liebman/esp32-gps-ntp/main/NTP.cpp

/*
 * MIT License
 *
 * Copyright (c) 2020 Christopher B. Liebman
 *
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
 * THE SOFTWARE IS PROVIDED "AS IS", WITHOUT WARRANTY OF ANY KIND, EXPRESS OR
 * IMPLIED, INCLUDING BUT NOT LIMITED TO THE WARRANTIES OF MERCHANTABILITY,
 * FITNESS FOR A PARTICULAR PURPOSE AND NONINFRINGEMENT. IN NO EVENT SHALL THE
 * AUTHORS OR COPYRIGHT HOLDERS BE LIABLE FOR ANY CLAIM, DAMAGES OR OTHER
 * LIABILITY, WHETHER IN AN ACTION OF CONTRACT, TORT OR OTHERWISE, ARISING FROM,
 * OUT OF OR IN CONNECTION WITH THE SOFTWARE OR THE USE OR OTHER DEALINGS IN THE
 * SOFTWARE.
*/

#include "NTP.h"
#include "Network.h"
#include "esp_log.h"
#include "math.h"

#include "lwip/err.h"
#include "lwip/sockets.h"
#include "lwip/sys.h"
#include <lwip/netdb.h>

static const char* TAG = "NTP";

//#define NTP_PACKET_DEBUG

#ifndef NTP_TASK_PRI
#define NTP_TASK_PRI configMAX_PRIORITIES-3
#endif

#ifndef NTP_TASK_CORE
#define NTP_TASK_CORE 1
#endif

//#define NTP_PACKET_DEBUG

#define NTP_PORT               123
#define PRECISION_COUNT        10000

typedef struct ntp_packet
{
    uint8_t  flags;
    uint8_t  stratum;
    uint8_t  poll;
    int8_t   precision;
    uint32_t delay;
    uint32_t dispersion;
    uint8_t  ref_id[4];
    NTPTime  ref_time;
    NTPTime  orig_time;
    NTPTime  recv_time;
    NTPTime  xmit_time;
} NTPPacket;

#define LI_NONE         0
#define LI_SIXTY_ONE    1
#define LI_FIFTY_NINE   2
#define LI_NOSYNC       3

#define MODE_RESERVED   0
#define MODE_ACTIVE     1
#define MODE_PASSIVE    2
#define MODE_CLIENT     3
#define MODE_SERVER     4
#define MODE_BROADCAST  5
#define MODE_CONTROL    6
#define MODE_PRIVATE    7

#define NTP_VERSION     4

#define REF_ID          "PPS "  // "GPS " when we have one!

#define setLI(value)    ((value&0x03)<<6)
#define setVERS(value)  ((value&0x07)<<3)
#define setMODE(value)  ((value&0x07))

#define getLI(value)    ((value>>6)&0x03)
#define getVERS(value)  ((value>>3)&0x07)
#define getMODE(value)  (value&0x07)

#define SEVENTY_YEARS   2208988800L
#define toEPOCH(t)      ((uint32_t)t-SEVENTY_YEARS)
#define toNTP(t)        ((uint32_t)t+SEVENTY_YEARS)

#ifdef NTP_PACKET_DEBUG
#include <time.h>
char* timestr(long int t)
{
    t = toEPOCH(t);
    return ctime(&t);
}

void dumpNTPPacket(NTPPacket* ntp)
{
    ESP_LOGI(TAG, "size:       %u", sizeof(*ntp));
    ESP_LOGI(TAG, "firstbyte:  0x%02x", *(uint8_t*)ntp);
    ESP_LOGI(TAG, "li:         %u", getLI(ntp->flags));
    ESP_LOGI(TAG, "version:    %u", getVERS(ntp->flags));
    ESP_LOGI(TAG, "mode:       %u", getMODE(ntp->flags));
    ESP_LOGI(TAG, "stratum:    %u", ntp->stratum);
    ESP_LOGI(TAG, "poll:       %u", ntp->poll);
    ESP_LOGI(TAG, "precision:  %d", ntp->precision);
    ESP_LOGI(TAG, "delay:      %u", ntp->delay);
    ESP_LOGI(TAG, "dispersion: %u", ntp->dispersion);
    ESP_LOGI(TAG, "ref_id:     %02x:%02x:%02x:%02x", ntp->ref_id[0], ntp->ref_id[1], ntp->ref_id[2], ntp->ref_id[3]);
    ESP_LOGI(TAG, "ref_time:   %08x:%08x", ntp->ref_time.seconds, ntp->ref_time.fraction);
    ESP_LOGI(TAG, "orig_time:  %08x:%08x", ntp->orig_time.seconds, ntp->orig_time.fraction);
    ESP_LOGI(TAG, "recv_time:  %08x:%08x", ntp->recv_time.seconds, ntp->recv_time.fraction);
    ESP_LOGI(TAG, "xmit_time:  %08x:%08x", ntp->xmit_time.seconds, ntp->xmit_time.fraction);
}
#else
#define dumpNTPPacket(x)
#endif


NTP::NTP(PPS& pps)
: _pps(pps)
{
}

NTP::~NTP()
{
}

void NTP::begin()
{
    _precision = computePrecision();
    xTaskCreatePinnedToCore(&NTP::task, "NTP", 4096, this, NTP_TASK_PRI, nullptr, NTP_TASK_CORE);
}

int8_t NTP::computePrecision()
{
    NTPTime t;
    uint64_t start = esp_timer_get_time();
    for (int i = 0; i < PRECISION_COUNT; ++i)
    {
        getNTPTime(&t);
    }
    uint64_t end = esp_timer_get_time();
    double        total = (double)(end - start) / 1000000.0;
    double        time  = total / PRECISION_COUNT;
    double        prec  = log2(time);
    ESP_LOGI(TAG, "computePrecision: total:%f time:%f prec:%f (%d)", total, time, prec, (int8_t)prec);
    return (int8_t)prec;
}

#define us2s(x) (((double)x)/(double)1000000) // microseconds to seconds

void NTP::getNTPTime(NTPTime* time)
{
    struct timeval tv;
    _pps.getTime(&tv);
    time->seconds = toNTP(tv.tv_sec);
    double percent = us2s(tv.tv_usec);
    time->fraction = (uint32_t)(percent * (double)4294967296L);
}


void NTP::task(void* data)
{
    NTP* ntp = static_cast<NTP*>(data);
    ESP_LOGI(TAG, "::task started with priority %d core %d", uxTaskPriorityGet(nullptr), xPortGetCoreID());
    int addr_family = AF_INET;
    int ip_protocol = IPPROTO_IP;
    char addr_str[128];
    NTPPacket packet;
    NTPTime   recv_time;

    while(true)
    {
        struct sockaddr_in dest_addr;
        dest_addr.sin_addr.s_addr = htonl(INADDR_ANY);
        dest_addr.sin_family = AF_INET;
        dest_addr.sin_port = htons(NTP_PORT);
        inet_ntoa_r(dest_addr.sin_addr, addr_str, sizeof(addr_str) - 1);

        // wait till there is a network connected
        Network::getNetwork().waitFor(Network::HAS_IP);

        int sock = socket(addr_family, SOCK_DGRAM, ip_protocol);
        if (sock < 0) {
            ESP_LOGE(TAG, "Unable to create socket: errno %d", errno);
            break;
        }
        ESP_LOGI(TAG, "Socket created");

        int err = bind(sock, (struct sockaddr *)&dest_addr, sizeof(dest_addr));
        if (err < 0) {
            ESP_LOGE(TAG, "Socket unable to bind: errno %d", errno);
            break;
        }
        ESP_LOGI(TAG, "Socket bound, port %d", NTP_PORT);

        while(true)
        {
            ESP_LOGD(TAG, "Waiting for data");
            struct sockaddr_in6 source_addr; // Large enough for both IPv4 or IPv6
            socklen_t socklen = sizeof(source_addr);
            int len = recvfrom(sock, &packet, sizeof(packet), 0, (struct sockaddr *)&source_addr, &socklen);
            ntp->getNTPTime(&recv_time);
            ntp->_req_count++;

            // Error occurred during receiving
            if (len < 0) {
                ESP_LOGE(TAG, "recvfrom failed: errno %d", errno);
                break;
            }
            if (len != sizeof(packet))
            {
                ESP_LOGE(TAG, "bad packet size: %u != %u", len, sizeof(packet));
                continue;
            }

            // Get the sender's ip address as string
            if (source_addr.sin6_family == PF_INET)
            {
                inet_ntoa_r(((struct sockaddr_in *)&source_addr)->sin_addr.s_addr, addr_str, sizeof(addr_str) - 1);
            }
            else if (source_addr.sin6_family == PF_INET6)
            {
                inet6_ntoa_r(source_addr.sin6_addr, addr_str, sizeof(addr_str) - 1);
            }
            ESP_LOGD(TAG, "Received %d bytes from %s:", len, addr_str);

            packet.delay              = ntohl(packet.delay);
            packet.dispersion         = ntohl(packet.dispersion);
            packet.orig_time.seconds  = ntohl(packet.orig_time.seconds);
            packet.orig_time.fraction = ntohl(packet.orig_time.fraction);
            packet.ref_time.seconds   = ntohl(packet.ref_time.seconds);
            packet.ref_time.fraction  = ntohl(packet.ref_time.fraction);
            packet.recv_time.seconds  = ntohl(packet.recv_time.seconds);
            packet.recv_time.fraction = ntohl(packet.recv_time.fraction);
            packet.xmit_time.seconds  = ntohl(packet.xmit_time.seconds);
            packet.xmit_time.fraction = ntohl(packet.xmit_time.fraction);
            dumpNTPPacket(&packet);
            //
            // Build the response
            //
            packet.flags      = setLI(LI_NONE) | setVERS(NTP_VERSION) | setMODE(MODE_SERVER);
            packet.stratum    = 1;
            packet.precision  = ntp->_precision;
            // TODO: compute actual root delay, and root dispersion
            packet.delay = 1;      //(uint32)(0.000001 * 65536.0);
            packet.dispersion = 1; //(uint32_t)(_gps.getDispersion() * 65536.0); // TODO: pre-calculate this?
            memcpy((char*)packet.ref_id, REF_ID, sizeof(packet.ref_id));
            packet.orig_time  = packet.xmit_time;
            packet.recv_time  = recv_time;
            ntp->getNTPTime(&(packet.ref_time));
            dumpNTPPacket(&packet);
            packet.delay              = htonl(packet.delay);
            packet.dispersion         = htonl(packet.dispersion);
            packet.orig_time.seconds  = htonl(packet.orig_time.seconds);
            packet.orig_time.fraction = htonl(packet.orig_time.fraction);
            packet.ref_time.seconds   = htonl(packet.ref_time.seconds);
            packet.ref_time.fraction  = htonl(packet.ref_time.fraction);
            packet.recv_time.seconds  = htonl(packet.recv_time.seconds);
            packet.recv_time.fraction = htonl(packet.recv_time.fraction);
            ntp->getNTPTime(&(packet.xmit_time));
            packet.xmit_time.seconds  = htonl(packet.xmit_time.seconds);
            packet.xmit_time.fraction = htonl(packet.xmit_time.fraction);

            err = sendto(sock, &packet, sizeof(packet), 0, (struct sockaddr *)&source_addr, sizeof(source_addr));
            if (err < 0)
            {
                ESP_LOGE(TAG, "Error occurred during sending: errno %d", errno);
                break;
            }
            ntp->_rsp_count++;
        }

        ESP_LOGE(TAG, "Shutting down socket and restarting...");
        shutdown(sock, 0);
        close(sock);
    }
}
